mytchel/trackball/src/adns9800_srom_A5.h

const int ADNS_SROM_ID = 0xa5;
const unsigned char PROGMEM ADNS_SROM[3070] = 
{
0x03,
0xa5,
0x6d,
0x12,
0x65,
0x99,
0x1e,
0xbe,
0xdf,
0x1c,
0xb8,
0xf2,
0x47,
0x0c,
0x9a,
0x97,
0x8d,
0x79,
0x51,
0x01,
0x8e,
0x81,
0x8a,
0x8e,
0x93,
0xbe,
0xdf,
0x3c,
0xdb,
0x34,
0xea,
0x56,
0x2e,
0xde,
0x1f,
0x9d,
0xb8,
0xf2,
0x41,
0xea,
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
};
