mytchel/trackball/src/adns_srom.h

/* Taken from https://github.com/mrjohnk/ADNS-9800 */

const uint8_t ADNS_SROM_ID = 0xa6;
const unsigned char PROGMEM ADNS_SROM[3070] = 
{
0x03,
0xa6,
0x68,
0x1e,
0x7d,
0x10,
0x7e,
0x7e,
0x5f,
0x1c,
0xb8,
0xf2,
0x47,
0x0c,
0x7b,
0x74,
0x4b,
0x14,
0x8b,
0x75,
0x66,
0x51,
0x0b,
0x8c,
0x76,
0x74,
0x4b,
0x14,
0xaa,
0xd6,
0x0f,
0x9c,
0xba,
0xf6,
0x6e,
0x3f,
0xdd,
0x38,
0xd5,
0x02,
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
};
